bbakersmith/egdab/graphic/exports/soldermask-2b.png

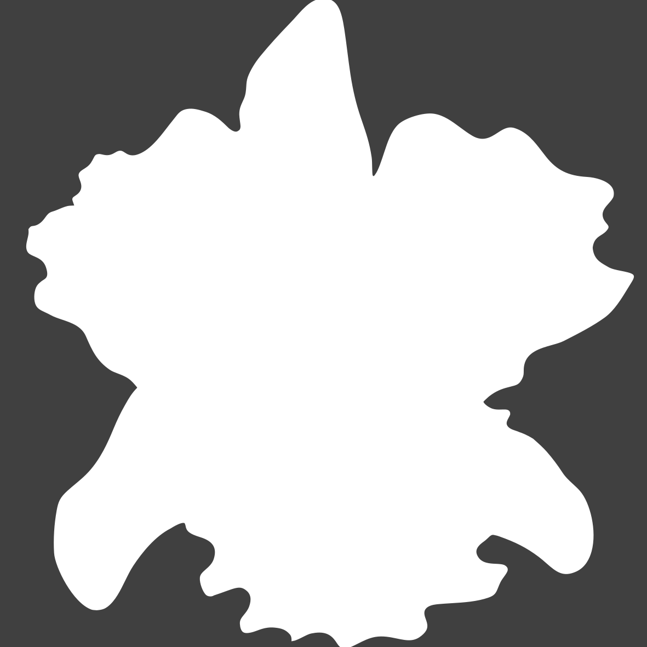
graphic/exports/soldermask-2b.png
