bbakersmith/egdab/graphic/exports/soldermask-2d.png

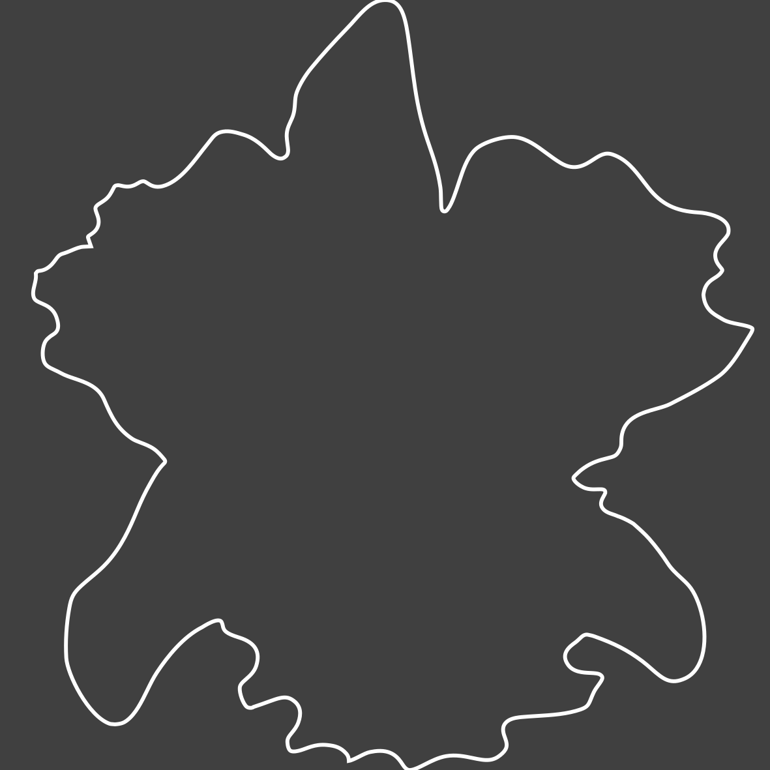
graphic/exports/soldermask-2d.png
