bbakersmith/egdab/graphic/exports/soldermask-2e.png

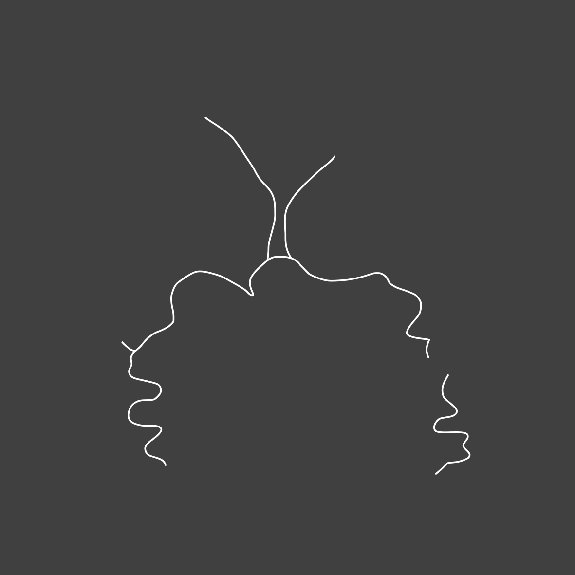
graphic/exports/soldermask-2e.png
