bbakersmith/egdab/graphic/exports/soldermask-2f.png

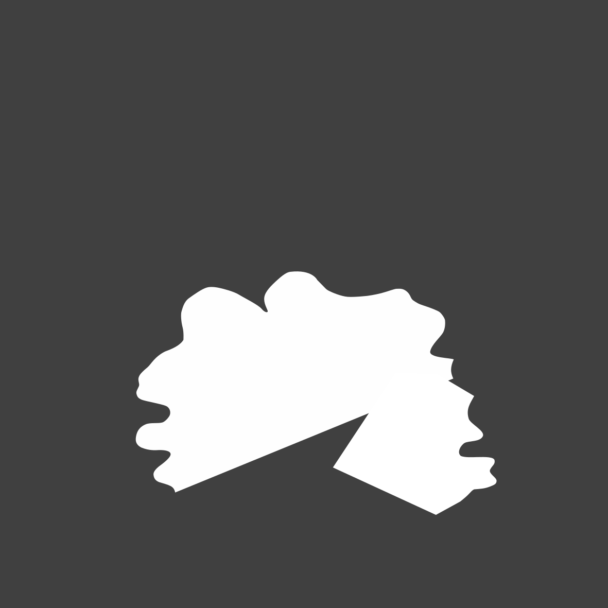
graphic/exports/soldermask-2f.png
